hotelcaliforniabm/duxel/sub-projects/shower/duxel_shower.textures/_Wood_Cherry_Original_1.jpg

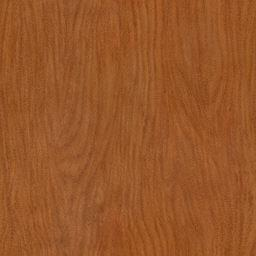
sub-projects/shower/duxel_shower.textures/_Wood_Cherry_Original_1.jpg
