hotelcaliforniabm/duxel/sub-projects/shower/duxel_shower.textures/_Wood_Veneer_02_.jpg

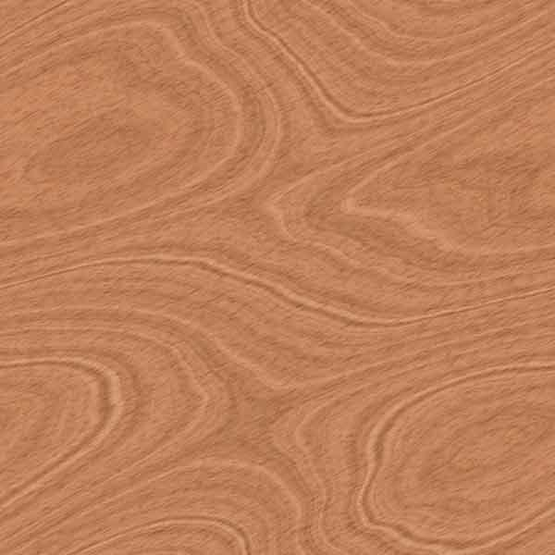
sub-projects/shower/duxel_shower.textures/_Wood_Veneer_02_.jpg
