hotelcaliforniabm/duxel/sub-projects/shower/duxel_shower.textures/Bamboo.jpg

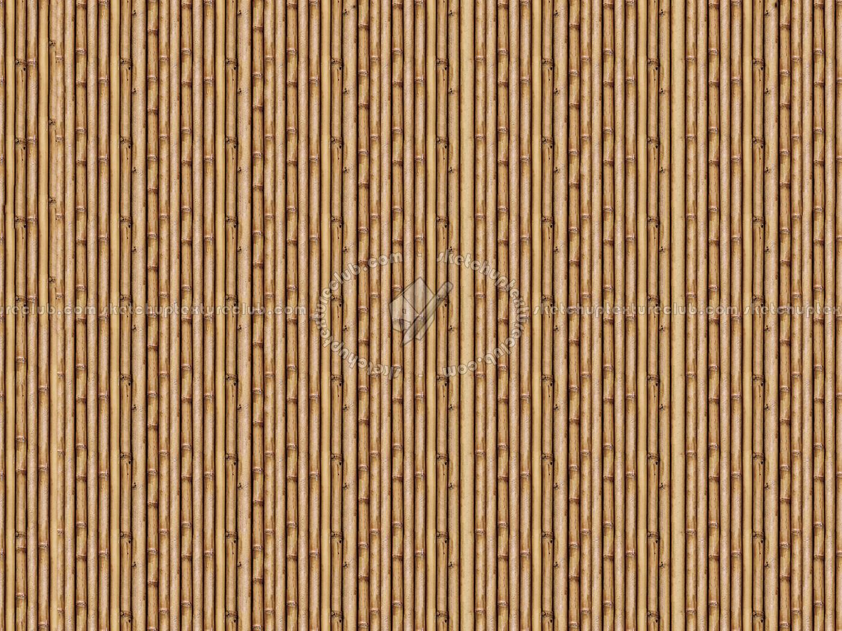
sub-projects/shower/duxel_shower.textures/Bamboo.jpg
