hotelcaliforniabm/duxel/sub-projects/shower/duxel_shower.textures/shower_bag.jpg

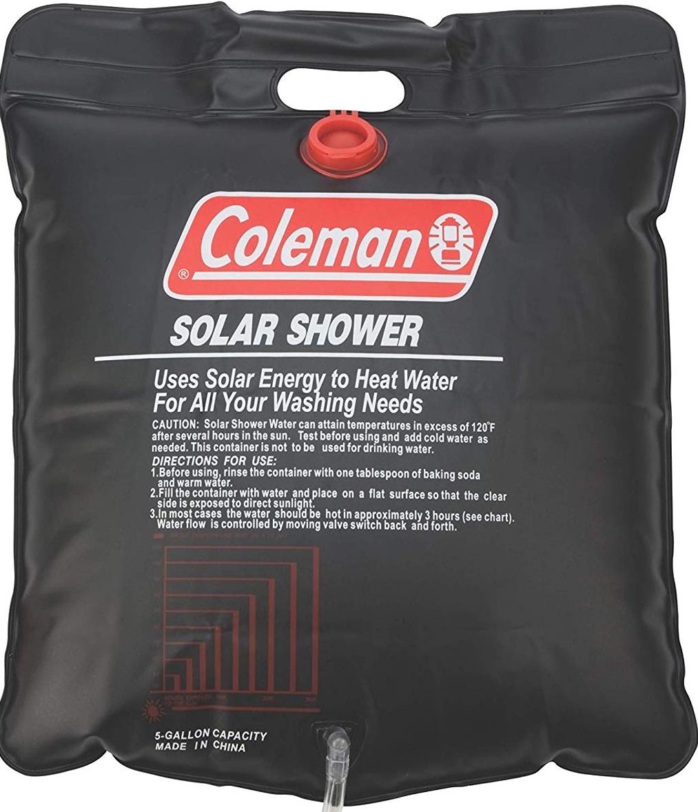
sub-projects/shower/duxel_shower.textures/shower_bag.jpg
