hotelcaliforniabm/duxel/sub-projects/shower/shower_pan.jpg

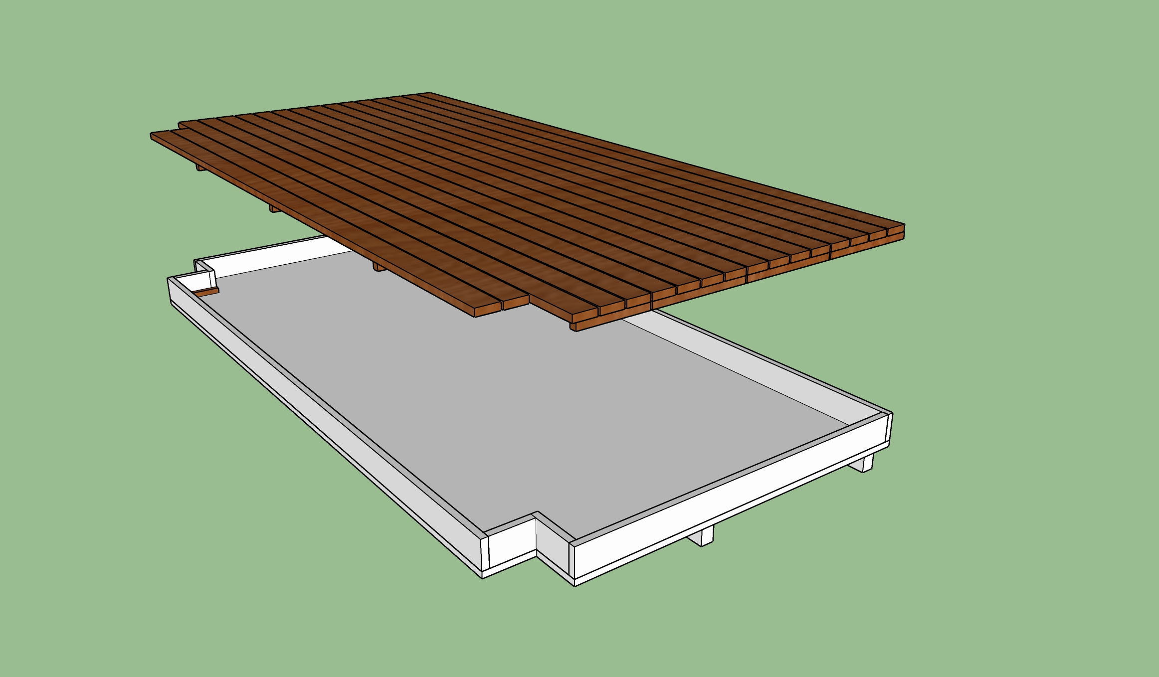
sub-projects/shower/shower_pan.jpg
