hotelcaliforniabm/duxel/sub-projects/stage truss mounts/photos/61149596_10219610109706703_1658331506285740032_o.jpg

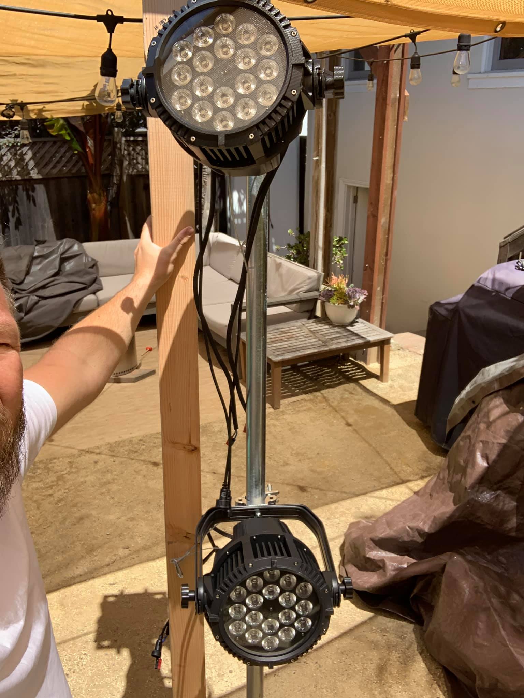
sub-projects/stage truss mounts/photos/61149596_10219610109706703_1658331506285740032_o.jpg
