hotelcaliforniabm/duxel/sub-projects/stage truss mounts/photos/61155196_10219610109146689_3591819091662340096_o.jpg

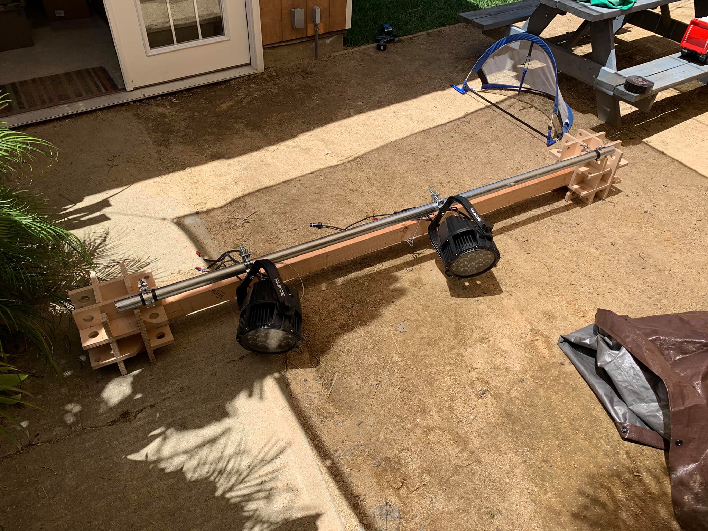
sub-projects/stage truss mounts/photos/61155196_10219610109146689_3591819091662340096_o.jpg
