hotelcaliforniabm/duxel/sub-projects/stage truss mounts/photos/61291276_10219610110626726_8642268858696073216_o.jpg

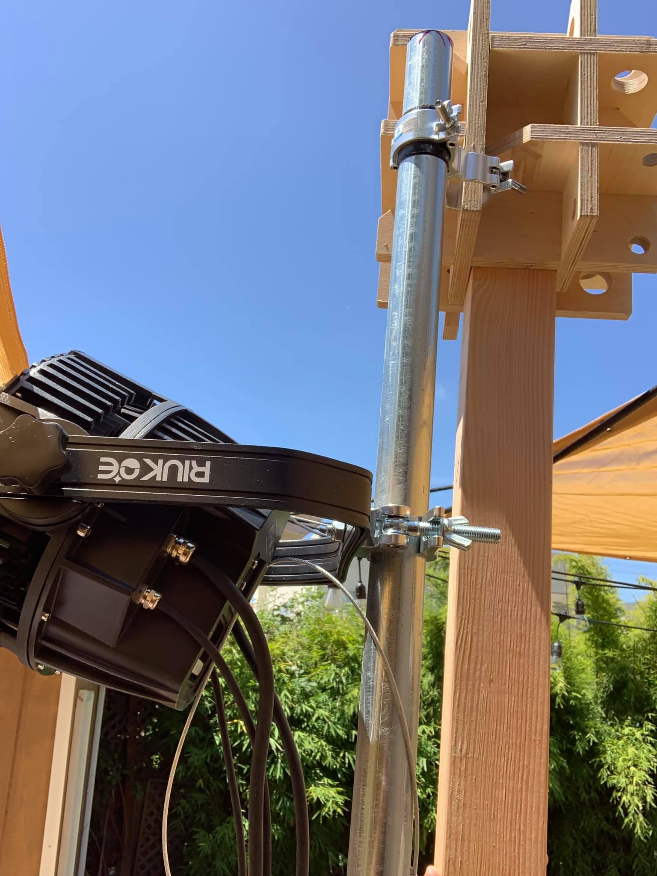
sub-projects/stage truss mounts/photos/61291276_10219610110626726_8642268858696073216_o.jpg
