hotelcaliforniabm/duxel/sub-projects/stage truss mounts/photos/61316921_10219610107346644_3035542460857057280_o.jpg

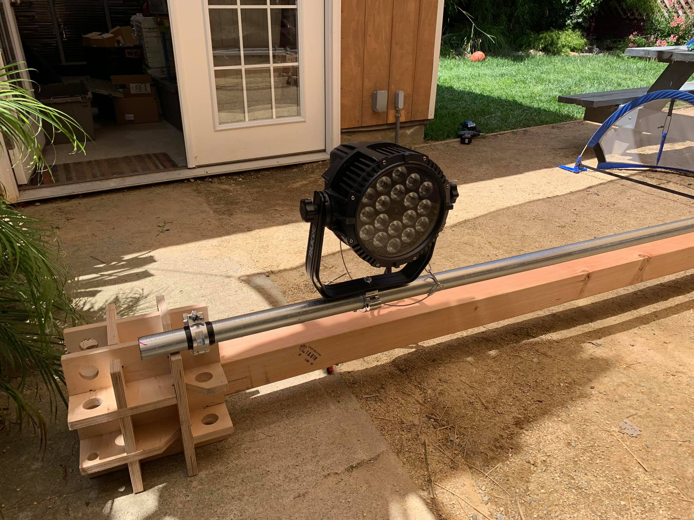
sub-projects/stage truss mounts/photos/61316921_10219610107346644_3035542460857057280_o.jpg
