hotelcaliforniabm/duxel/sub-projects/stage truss mounts/photos/61429488_10219610110106713_4438708066006859776_o.jpg

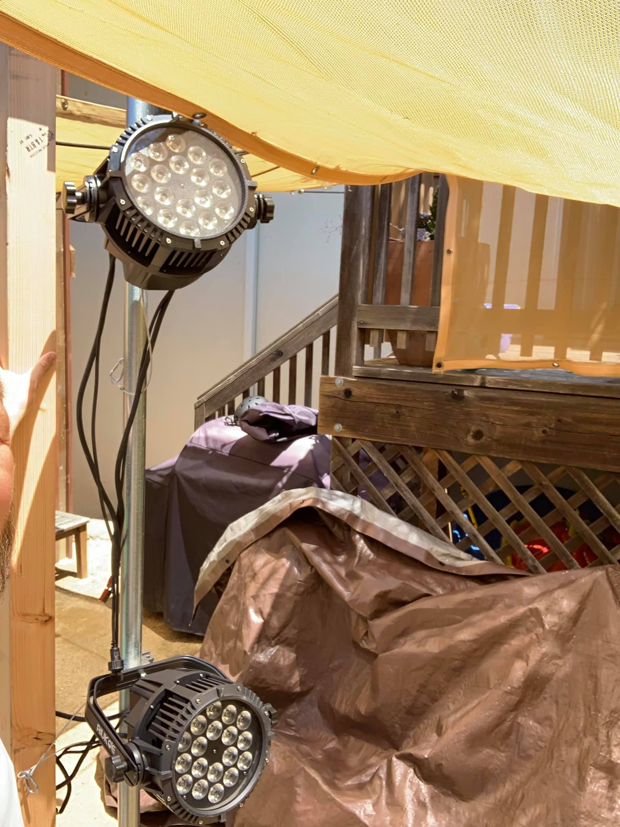
sub-projects/stage truss mounts/photos/61429488_10219610110106713_4438708066006859776_o.jpg
