hotelcaliforniabm/duxel/sub-projects/stage truss mounts/photos/61451495_10219610112106763_7335452113163517952_o.jpg

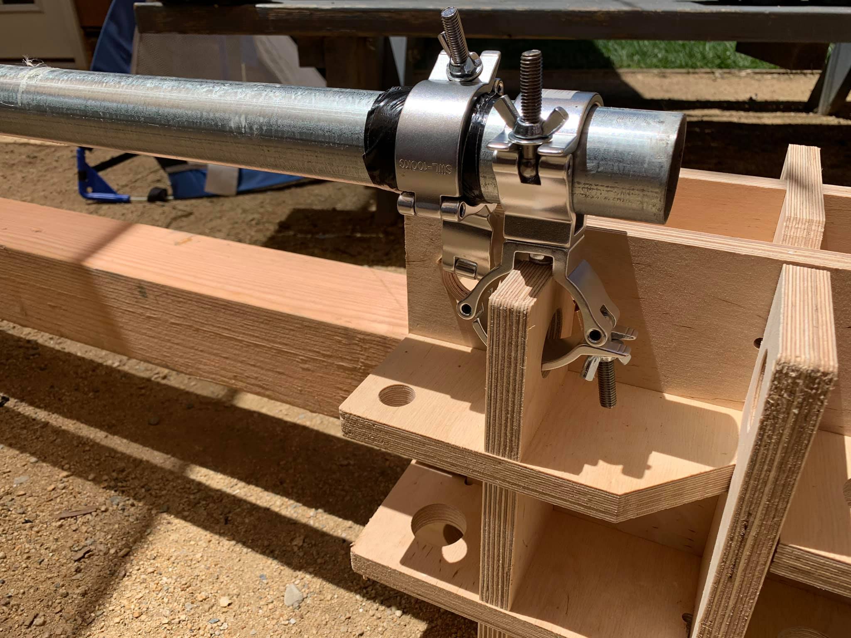
sub-projects/stage truss mounts/photos/61451495_10219610112106763_7335452113163517952_o.jpg
